vyges/vyges-edge-sensor-soc/docs/user_project_wrapper_floorplan.png

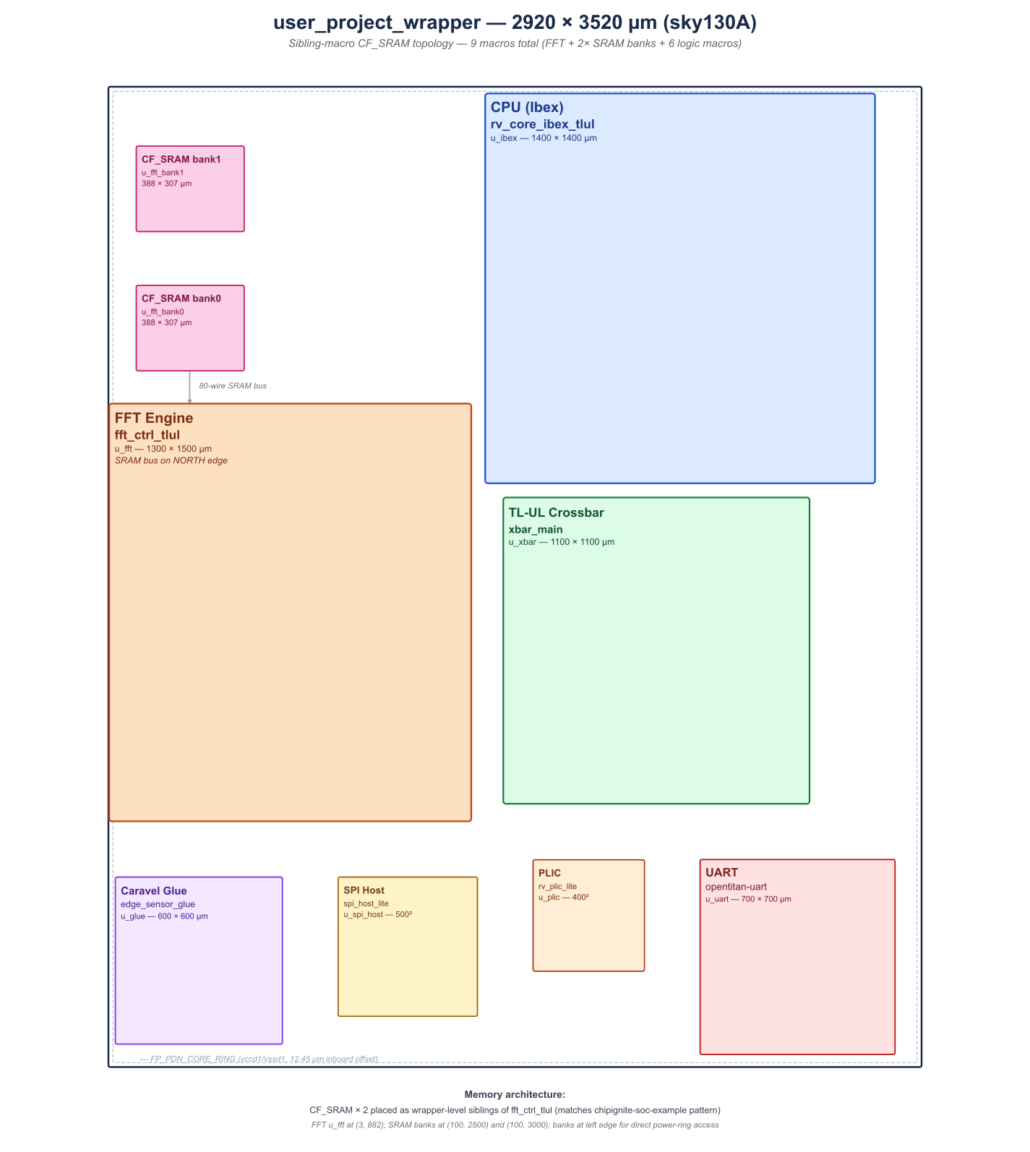
docs/user_project_wrapper_floorplan.png
