vyges/vyges-edge-sensor-soc/pcba/asic/edge_sensor_asic.kicad_sch

## KiCad design pcba/asic/edge_sensor_asic.kicad_sch (2026-04-12)

Schematic: edge_sensor_asic.kicad_sch

Parts:
D1: led_green_0603; LED_0603_1608Metric
J1: usb_c_receptacle; USB_C_Receptacle_HRO_TYPE-C-31-M-12
J2: pmod_2x6_female; PinSocket_2x06_P2.54mm_Vertical
J3: tag_connect_10pin; PinHeader_2x05_P2.54mm_Vertical
SW1: reset_button_smd; SW_SPST_B3U-1000P
U1: caravel_qfn64; QFN-64-1EP_9x9mm_P0.5mm_EP7.65x7.65mm
U2: ft232h; LQFP-48_7x7mm_P0.5mm
U3: w25q32jvssiq; SOIC-8_5.23x5.23mm_P1.27mm
U4: AP7361C-18E (1.8V); SOT-223-3_TabPin2
U5: AP7361C-33E (3.3V); SOT-223-3_TabPin2
U6: MCP809-300 (reset supervisor); SOT-23
