vyges/vyges-edge-sensor-soc/pcba/fpga/edge_sensor_fpga.kicad_sch

## KiCad design pcba/fpga/edge_sensor_fpga.kicad_sch (2026-04-12)

Schematic: edge_sensor_fpga.kicad_sch

Parts:
D1: led_green_0603; LED_0603_1608Metric
J1: pmod_2x6_male; PinHeader_2x06_P2.54mm_Vertical
J2: pmod_2x6_female; PinSocket_2x06_P2.54mm_Vertical
R1: 10k; R_0402_1005Metric
