vyges/vyges-edge-sensor-soc/verilog/gl/user_project_wrapper.v

module user_project_wrapper (user_clock2,
    wb_clk_i,
    wb_rst_i,
    wbs_ack_o,
    wbs_cyc_i,
    wbs_stb_i,
    wbs_we_i,
    vssa2,
    vdda2,
    vssa1,
    vdda1,
    vssd2,
    vccd2,
    vssd1,
    vccd1,
    analog_io,
    io_in,
    io_oeb,
    io_out,
    la_data_in,
    la_data_out,
    la_oenb,
    user_irq,
    wbs_adr_i,
    wbs_dat_i,
    wbs_dat_o,
    wbs_sel_i);
 input user_clock2;
 input wb_clk_i;
 input wb_rst_i;
 output wbs_ack_o;
 input wbs_cyc_i;
 input wbs_stb_i;
 input wbs_we_i;
 inout vssa2;
 inout vdda2;
 inout vssa1;
 inout vdda1;
 inout vssd2;
 inout vccd2;
 inout vssd1;
 inout vccd1;
 inout [28:0] analog_io;
 input [37:0] io_in;
 output [37:0] io_oeb;
 output [37:0] io_out;
 input [127:0] la_data_in;
 output [127:0] la_data_out;
 input [127:0] la_oenb;
 output [2:0] user_irq;
 input [31:0] wbs_adr_i;
 input [31:0] wbs_dat_i;
 output [31:0] wbs_dat_o;
 input [3:0] wbs_sel_i;

 wire clk;
 wire fft_done;
 wire fft_error;
 wire \fft_sram_addr[0] ;
 wire \fft_sram_addr[1] ;
 wire \fft_sram_addr[2] ;
 wire \fft_sram_addr[3] ;
 wire \fft_sram_addr[4] ;
 wire \fft_sram_addr[5] ;
 wire \fft_sram_addr[6] ;
 wire \fft_sram_addr[7] ;
 wire \fft_sram_addr[8] ;
 wire \fft_sram_addr[9] ;
 wire \fft_sram_ben[0] ;
 wire \fft_sram_ben[10] ;
 wire \fft_sram_ben[11] ;
 wire \fft_sram_ben[12] ;
 wire \fft_sram_ben[13] ;
 wire \fft_sram_ben[14] ;
 wire \fft_sram_ben[15] ;
 wire \fft_sram_ben[16] ;
 wire \fft_sram_ben[17] ;
 wire \fft_sram_ben[18] ;
 wire \fft_sram_ben[19] ;
 wire \fft_sram_ben[1] ;
 wire \fft_sram_ben[20] ;
 wire \fft_sram_ben[21] ;
 wire \fft_sram_ben[22] ;
 wire \fft_sram_ben[23] ;
 wire \fft_sram_ben[24] ;
 wire \fft_sram_ben[25] ;
 wire \fft_sram_ben[26] ;
 wire \fft_sram_ben[27] ;
 wire \fft_sram_ben[28] ;
 wire \fft_sram_ben[29] ;
 wire \fft_sram_ben[2] ;
 wire \fft_sram_ben[30] ;
 wire \fft_sram_ben[31] ;
 wire \fft_sram_ben[3] ;
 wire \fft_sram_ben[4] ;
 wire \fft_sram_ben[5] ;
 wire \fft_sram_ben[6] ;
 wire \fft_sram_ben[7] ;
 wire \fft_sram_ben[8] ;
 wire \fft_sram_ben[9] ;
 wire fft_sram_clk;
 wire \fft_sram_en[0] ;
 wire \fft_sram_en[1] ;
 wire \fft_sram_rdata0[0] ;
 wire \fft_sram_rdata0[10] ;
 wire \fft_sram_rdata0[11] ;
 wire \fft_sram_rdata0[12] ;
 wire \fft_sram_rdata0[13] ;
 wire \fft_sram_rdata0[14] ;
 wire \fft_sram_rdata0[15] ;
 wire \fft_sram_rdata0[16] ;
 wire \fft_sram_rdata0[17] ;
 wire \fft_sram_rdata0[18] ;
 wire \fft_sram_rdata0[19] ;
 wire \fft_sram_rdata0[1] ;
 wire \fft_sram_rdata0[20] ;
 wire \fft_sram_rdata0[21] ;
 wire \fft_sram_rdata0[22] ;
 wire \fft_sram_rdata0[23] ;
 wire \fft_sram_rdata0[24] ;
 wire \fft_sram_rdata0[25] ;
 wire \fft_sram_rdata0[26] ;
 wire \fft_sram_rdata0[27] ;
 wire \fft_sram_rdata0[28] ;
 wire \fft_sram_rdata0[29] ;
 wire \fft_sram_rdata0[2] ;
 wire \fft_sram_rdata0[30] ;
 wire \fft_sram_rdata0[31] ;
 wire \fft_sram_rdata0[3] ;
 wire \fft_sram_rdata0[4] ;
 wire \fft_sram_rdata0[5] ;
 wire \fft_sram_rdata0[6] ;
 wire \fft_sram_rdata0[7] ;
 wire \fft_sram_rdata0[8] ;
 wire \fft_sram_rdata0[9] ;
 wire \fft_sram_rdata1[0] ;
 wire \fft_sram_rdata1[10] ;
 wire \fft_sram_rdata1[11] ;
 wire \fft_sram_rdata1[12] ;
 wire \fft_sram_rdata1[13] ;
 wire \fft_sram_rdata1[14] ;
 wire \fft_sram_rdata1[15] ;
 wire \fft_sram_rdata1[16] ;
 wire \fft_sram_rdata1[17] ;
 wire \fft_sram_rdata1[18] ;
 wire \fft_sram_rdata1[19] ;
 wire \fft_sram_rdata1[1] ;
 wire \fft_sram_rdata1[20] ;
 wire \fft_sram_rdata1[21] ;
 wire \fft_sram_rdata1[22] ;
 wire \fft_sram_rdata1[23] ;
 wire \fft_sram_rdata1[24] ;
 wire \fft_sram_rdata1[25] ;
 wire \fft_sram_rdata1[26] ;
 wire \fft_sram_rdata1[27] ;
 wire \fft_sram_rdata1[28] ;
 wire \fft_sram_rdata1[29] ;
 wire \fft_sram_rdata1[2] ;
 wire \fft_sram_rdata1[30] ;
 wire \fft_sram_rdata1[31] ;
 wire \fft_sram_rdata1[3] ;
 wire \fft_sram_rdata1[4] ;
 wire \fft_sram_rdata1[5] ;
 wire \fft_sram_rdata1[6] ;
 wire \fft_sram_rdata1[7] ;
 wire \fft_sram_rdata1[8] ;
 wire \fft_sram_rdata1[9] ;
 wire fft_sram_rwb;
 wire \fft_sram_wdata[0] ;
 wire \fft_sram_wdata[10] ;
 wire \fft_sram_wdata[11] ;
 wire \fft_sram_wdata[12] ;
 wire \fft_sram_wdata[13] ;
 wire \fft_sram_wdata[14] ;
 wire \fft_sram_wdata[15] ;
 wire \fft_sram_wdata[16] ;
 wire \fft_sram_wdata[17] ;
 wire \fft_sram_wdata[18] ;
 wire \fft_sram_wdata[19] ;
 wire \fft_sram_wdata[1] ;
 wire \fft_sram_wdata[20] ;
 wire \fft_sram_wdata[21] ;
 wire \fft_sram_wdata[22] ;
 wire \fft_sram_wdata[23] ;
 wire \fft_sram_wdata[24] ;
 wire \fft_sram_wdata[25] ;
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
    \fft_sram_ben[18] ,
    \fft_sram_ben[17] ,
    \fft_sram_ben[16] ,
    \fft_sram_ben[15] ,
    \fft_sram_ben[14] ,
    \fft_sram_ben[13] ,
    \fft_sram_ben[12] ,
    \fft_sram_ben[11] ,
    \fft_sram_ben[10] ,
    \fft_sram_ben[9] ,
    \fft_sram_ben[8] ,
    \fft_sram_ben[7] ,
    \fft_sram_ben[6] ,
    \fft_sram_ben[5] ,
    \fft_sram_ben[4] ,
    \fft_sram_ben[3] ,
    \fft_sram_ben[2] ,
    \fft_sram_ben[1] ,
    \fft_sram_ben[0] }),
    .DI({\fft_sram_wdata[31] ,
    \fft_sram_wdata[30] ,
    \fft_sram_wdata[29] ,
    \fft_sram_wdata[28] ,
    \fft_sram_wdata[27] ,
    \fft_sram_wdata[26] ,
    \fft_sram_wdata[25] ,
    \fft_sram_wdata[24] ,
    \fft_sram_wdata[23] ,
    \fft_sram_wdata[22] ,
    \fft_sram_wdata[21] ,
    \fft_sram_wdata[20] ,
    \fft_sram_wdata[19] ,
    \fft_sram_wdata[18] ,
    \fft_sram_wdata[17] ,
    \fft_sram_wdata[16] ,
    \fft_sram_wdata[15] ,
    \fft_sram_wdata[14] ,
    \fft_sram_wdata[13] ,
    \fft_sram_wdata[12] ,
    \fft_sram_wdata[11] ,
    \fft_sram_wdata[10] ,
    \fft_sram_wdata[9] ,
    \fft_sram_wdata[8] ,
    \fft_sram_wdata[7] ,
    \fft_sram_wdata[6] ,
    \fft_sram_wdata[5] ,
    \fft_sram_wdata[4] ,
    \fft_sram_wdata[3] ,
    \fft_sram_wdata[2] ,
    \fft_sram_wdata[1] ,
    \fft_sram_wdata[0] }),
    .DO({\fft_sram_rdata1[31] ,
    \fft_sram_rdata1[30] ,
    \fft_sram_rdata1[29] ,
    \fft_sram_rdata1[28] ,
    \fft_sram_rdata1[27] ,
    \fft_sram_rdata1[26] ,
    \fft_sram_rdata1[25] ,
    \fft_sram_rdata1[24] ,
    \fft_sram_rdata1[23] ,
    \fft_sram_rdata1[22] ,
    \fft_sram_rdata1[21] ,
    \fft_sram_rdata1[20] ,
    \fft_sram_rdata1[19] ,
    \fft_sram_rdata1[18] ,
    \fft_sram_rdata1[17] ,
    \fft_sram_rdata1[16] ,
    \fft_sram_rdata1[15] ,
    \fft_sram_rdata1[14] ,
    \fft_sram_rdata1[13] ,
    \fft_sram_rdata1[12] ,
    \fft_sram_rdata1[11] ,
    \fft_sram_rdata1[10] ,
    \fft_sram_rdata1[9] ,
    \fft_sram_rdata1[8] ,
    \fft_sram_rdata1[7] ,
    \fft_sram_rdata1[6] ,
    \fft_sram_rdata1[5] ,
    \fft_sram_rdata1[4] ,
    \fft_sram_rdata1[3] ,
    \fft_sram_rdata1[2] ,
    \fft_sram_rdata1[1] ,
    \fft_sram_rdata1[0] }));
 edge_sensor_glue u_glue (.VGND(vssd1),
    .VPWR(vccd1),
    .clk_o(clk),
    .fft_done_i(fft_done),
    .fft_error_i(fft_error),
    .intr_spi_host_idle_i(intr_spi_host_idle),
    .intr_spi_host_rx_full_i(intr_spi_host_rx_full),
    .intr_spi_host_tx_empty_i(intr_spi_host_tx_empty),
    .intr_uart_rx_break_err_i(intr_uart_rx_break_err),
    .intr_uart_rx_frame_err_i(intr_uart_rx_frame_err),
    .intr_uart_rx_overflow_i(intr_uart_rx_overflow),
    .intr_uart_rx_parity_err_i(intr_uart_rx_parity_err),
    .intr_uart_rx_timeout_i(intr_uart_rx_timeout),
    .intr_uart_rx_watermark_i(intr_uart_rx_watermark),
    .intr_uart_tx_done_i(intr_uart_tx_done),
    .intr_uart_tx_empty_i(intr_uart_tx_empty),
    .intr_uart_tx_watermark_i(intr_uart_tx_watermark),
    .plic_irq_i(plic_irq),
    .rst_no(rst_n),
    .spi_cs_n_i(spi_cs_n),
    .spi_miso_o(spi_miso),
    .spi_mosi_i(spi_mosi),
    .spi_sclk_i(spi_sclk),
    .uart_rx_o(uart_rx),
    .uart_tx_i(uart_tx),
    .wb_clk_i(wb_clk_i),
    .wb_rst_i(wb_rst_i),
    .wbs_ack_o(wbs_ack_o),
    .wbs_cyc_i(wbs_cyc_i),
    .wbs_stb_i(wbs_stb_i),
    .wbs_we_i(wbs_we_i),
    .intr_vec_o({\intr_vec[31] ,
    \intr_vec[30] ,
    \intr_vec[29] ,
    \intr_vec[28] ,
    \intr_vec[27] ,
    \intr_vec[26] ,
    \intr_vec[25] ,
    \intr_vec[24] ,
    \intr_vec[23] ,
    \intr_vec[22] ,
    \intr_vec[21] ,
    \intr_vec[20] ,
    \intr_vec[19] ,
    \intr_vec[18] ,
    \intr_vec[17] ,
    \intr_vec[16] ,
    \intr_vec[15] ,
    \intr_vec[14] ,
    \intr_vec[13] ,
    \intr_vec[12] ,
    \intr_vec[11] ,
    \intr_vec[10] ,
    \intr_vec[9] ,
    \intr_vec[8] ,
    \intr_vec[7] ,
    \intr_vec[6] ,
    \intr_vec[5] ,
    \intr_vec[4] ,
    \intr_vec[3] ,
    \intr_vec[2] ,
    \intr_vec[1] ,
    \intr_vec[0] }),
    .io_in({io_in[37],
    io_in[36],
    io_in[35],
    io_in[34],
    io_in[33],
    io_in[32],
    io_in[31],
    io_in[30],
    io_in[29],
    io_in[28],
    io_in[27],
    io_in[26],
    io_in[25],
    io_in[24],
    io_in[23],
    io_in[22],
    io_in[21],
    io_in[20],
    io_in[19],
    io_in[18],
    io_in[17],
    io_in[16],
    io_in[15],
    io_in[14],
    io_in[13],
    io_in[12],
    io_in[11],
    io_in[10],
    io_in[9],
    io_in[8],
    io_in[7],
    io_in[6],
    io_in[5],
    io_in[4],
    io_in[3],
    io_in[2],
    io_in[1],
    io_in[0]}),
    .io_oeb({io_oeb[37],
    io_oeb[36],
    io_oeb[35],
    io_oeb[34],
    io_oeb[33],
    io_oeb[32],
    io_oeb[31],
    io_oeb[30],
    io_oeb[29],
    io_oeb[28],
    io_oeb[27],
    io_oeb[26],
    io_oeb[25],
    io_oeb[24],
    io_oeb[23],
    io_oeb[22],
    io_oeb[21],
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
    \tl_xbar_apb_h2d[27] ,
    \tl_xbar_apb_h2d[26] ,
    \tl_xbar_apb_h2d[25] ,
    \tl_xbar_apb_h2d[24] ,
    \tl_xbar_apb_h2d[23] ,
    \tl_xbar_apb_h2d[22] ,
    \tl_xbar_apb_h2d[21] ,
    \tl_xbar_apb_h2d[20] ,
    \tl_xbar_apb_h2d[19] ,
    \tl_xbar_apb_h2d[18] ,
    \tl_xbar_apb_h2d[17] ,
    \tl_xbar_apb_h2d[16] ,
    \tl_xbar_apb_h2d[15] ,
    \tl_xbar_apb_h2d[14] ,
    \tl_xbar_apb_h2d[13] ,
    \tl_xbar_apb_h2d[12] ,
    \tl_xbar_apb_h2d[11] ,
    \tl_xbar_apb_h2d[10] ,
    \tl_xbar_apb_h2d[9] ,
    \tl_xbar_apb_h2d[8] ,
    \tl_xbar_apb_h2d[7] ,
    \tl_xbar_apb_h2d[6] ,
    \tl_xbar_apb_h2d[5] ,
    \tl_xbar_apb_h2d[4] ,
    \tl_xbar_apb_h2d[3] ,
    \tl_xbar_apb_h2d[2] ,
    \tl_xbar_apb_h2d[1] ,
    \tl_xbar_apb_h2d[0] }));
 sky130_fd_sc_hd__conb_1 TIE_ZERO_zero_ (.VGND(vssd1),
    .VNB(vssd1),
    .VPB(vccd1),
    .VPWR(vccd1),
    .LO(zero_));
 sky130_fd_sc_hd__conb_1 TIE_ONE_one_ (.VGND(vssd1),
    .VNB(vssd1),
    .VPB(vccd1),
    .VPWR(vccd1),
    .HI(one_));
endmodule
